Caerbannog/hexabot/hexabot-dsPIC33.X/app_registers.c

/*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
    You should have received a copy of the GNU General Public License
    along with this program.  If not, see <http://www.gnu.org/licenses/>.
 */

#include "app_registers.h"
#include <usb/usb_commands.h>
#include <usb/usb_debug.h>
#include <string.h>
#include <xc.h>


#ifndef PORTA // 806 dsPIC
uint16_t PORTA = 0;
uint16_t LATA  = 0;
uint16_t TRISA = 0;
#endif

uint8_t servo1 = 127; // FIXME: register ?

float KP = 1.4; // 1/(m/s)
float KI = 1.0;
float KD = 0;

float dist_target = NAN;
float dist_target_speed = NAN;
float theta_target = NAN;
float theta_target_speed = NAN;

float r_target_speed = 0;
float l_target_speed = 0;
float r_control_speed = 0;
float l_control_speed = 0;
float asserv_interval = .005;

unsigned long qei3_position = 0;
unsigned long qei4_position = 0;
volatile unsigned int qei3_errors = 0;
volatile unsigned int qei4_errors = 0;

float odometry_x = 0;
float odometry_y = 0;
float odometry_dist = 0;
float odometry_dist_speed = 0;
float odometry_theta = 0;
float odometry_theta_speed = 0;
int odometry_interval = .005;

float odometry_r_arc = 15.07 / 8192;
float odometry_l_arc = 15.07 / 8192;
float odometry_rotation_imbalance = 0;
float odometry_half_wheel_distance = 14.2;

float motor_ticks_per_meter = 57000; // FIXME: Approximated. Encoder ticks per motor turn 6.25*500 = 3125, belt ratio=?
float motor_half_wheel_distance = 9.5;
bool stop_motors = 0;
float max_acceleration = 0.3; // m/(s^2)

const register_t registers[] = {
    // 0
    REG_VAR(PORTA), // Input.
    REG_VAR(PORTB),
    REG_VAR(PORTC),
    REG_VAR(PORTD),
    REG_VAR(PORTE),
    REG_VAR(PORTF),
    REG_VAR(PORTG),
    // 7
    REG_VAR(LATA), // Output.
    REG_VAR(LATB),
    REG_VAR(LATC),
    REG_VAR(LATD),
    REG_VAR(LATE),
    REG_VAR(LATF),
    REG_VAR(LATG),
    // 14
    REG_VAR(TRISA), // Pin direction.
    REG_VAR(TRISB),
    REG_VAR(TRISC),
    REG_VAR(TRISD),
    REG_VAR(TRISE),
    REG_VAR(TRISF),
    REG_VAR(TRISG),
    // 21
    REG_VAR(OC1RS), // MOTOR_R_PWM
    REG_VAR(OC2RS), // MOTOR_L_PWM
    REG_VAR(OC3RS), // SERVO_1
    REG_VAR(OC4RS), // SERVO_2
    // 25
    REG_VAR(ADC1BUF0), // SENSE_R
    REG_VAR(ADC1BUF1), // SENSE_L
    REG_VAR(ADC1BUF2), // AN3
    REG_VAR(ADC1BUF3), // VBAT
    // 29
    REG_VAR(POS1CNTL), // Low 16 bits of position counter for QEI1.
    REG_VAR(POS2CNTL), // Same for QEI2.
    // 31
    REG_VAR(KP),
    REG_VAR(KI),
    REG_VAR(KD),
    // 34
    REG_VAR(dist_target),
    REG_VAR(dist_target_speed),
    REG_VAR(theta_target),
    REG_VAR(theta_target_speed),
    // 38
    REG_VAR(r_target_speed),
    REG_VAR(l_target_speed),
    REG_VAR(r_control_speed),
    REG_VAR(l_control_speed),
    REG_VAR(asserv_interval),
    // 43
    REG_VAR(qei3_position),
    REG_VAR(qei4_position),
    REG_VAR(qei3_errors),
    REG_VAR(qei4_errors),
    // 47
    REG_VAR(odometry_x), // Estimated position
    REG_VAR(odometry_y), // Estimated position
    REG_VAR(odometry_dist), // Decreases when travelling backward
    REG_VAR(odometry_dist_speed),
    REG_VAR(odometry_theta), // Estimated absolute orientation
    REG_VAR(odometry_theta_speed),
    REG_VAR(odometry_interval),
    // 52
    REG_VAR(odometry_r_arc),
    REG_VAR(odometry_l_arc),
    REG_VAR(odometry_rotation_imbalance),
    REG_VAR(odometry_half_wheel_distance),
    // 56
    REG_VAR(motor_ticks_per_meter),
    REG_VAR(motor_half_wheel_distance),
    REG_VAR(stop_motors), // Set automatically on USB disconnects.
    REG_VAR(max_acceleration),
};

const uint8_t register_count = sizeof(registers) / sizeof(*registers);


void register_command(uint8_t * buffer, uint8_t received)
{
    uint8_t reg = buffer[0];
    if (reg >= register_count) {
        ERROR("reg=%d", reg);
        buffer[0] = COMMAND_ERROR;
    }
    else {
        uint8_t reg_size = registers[reg].size;
        if (received == 1) {
            memcpy(buffer, registers[reg].addr, reg_size);
            CommandInSend(buffer, reg_size);
            return;
        }
        else if (received - 1 != reg_size) {
            ERROR("reg=%d size is %d not %d", reg, reg_size, received - 1);
            buffer[0] = COMMAND_ERROR;
        }
        else {
            memcpy(registers[reg].addr, buffer + 1, received - 1);
            buffer[0] = COMMAND_SUCCESS;
        }
    }
    CommandInSend(buffer, 1);
}
