Caerbannog/hexabot/hexabot-dsPIC33.X/app_registers.h

/*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
    You should have received a copy of the GNU General Public License
    along with this program.  If not, see <http://www.gnu.org/licenses/>.
 */

#ifndef APP_REGISTERS_H
#define	APP_REGISTERS_H

#include <stdint.h>
#include <stdbool.h>

#define REG_VAR(var)     { (uint8_t *)&(var), sizeof(var) }
#define NAN              (0.0 / 0.0) // Not A Number is a special float value.
#define NOT_NAN(f)       (f == f)

typedef struct {
    uint8_t * const addr;
    const uint8_t size;
} register_t;

extern uint8_t servo1;

extern float KP;
extern float KI;
extern float KD;

extern float dist_target;
extern float dist_target_speed;
extern float theta_target;
extern float theta_target_speed;

extern float r_target_speed;
extern float l_target_speed;
extern float r_control_speed;
extern float l_control_speed;
extern float asserv_interval;

extern unsigned long qei3_position;
extern unsigned long qei4_position;
extern volatile unsigned int qei3_errors;
extern volatile unsigned int qei4_errors;

extern float odometry_x;
extern float odometry_y;
extern float odometry_dist;
extern float odometry_dist_speed;
extern float odometry_theta;
extern float odometry_theta_speed;
extern int odometry_interval;

extern float odometry_r_arc;
extern float odometry_l_arc;
extern float odometry_rotation_imbalance;
extern float odometry_half_wheel_distance;

extern float motor_ticks_per_meter;
extern float motor_half_wheel_distance;
extern bool stop_motors;
extern float max_acceleration;


void register_command(uint8_t * buffer, uint8_t received);

#endif	/* APP_REGISTERS_H */
